Estylos/VFD-MQTT/KICAD_FILES/VFD-MQTT.kicad_sch

## KiCad design KICAD_FILES/VFD-MQTT.kicad_sch (2022-10-23)

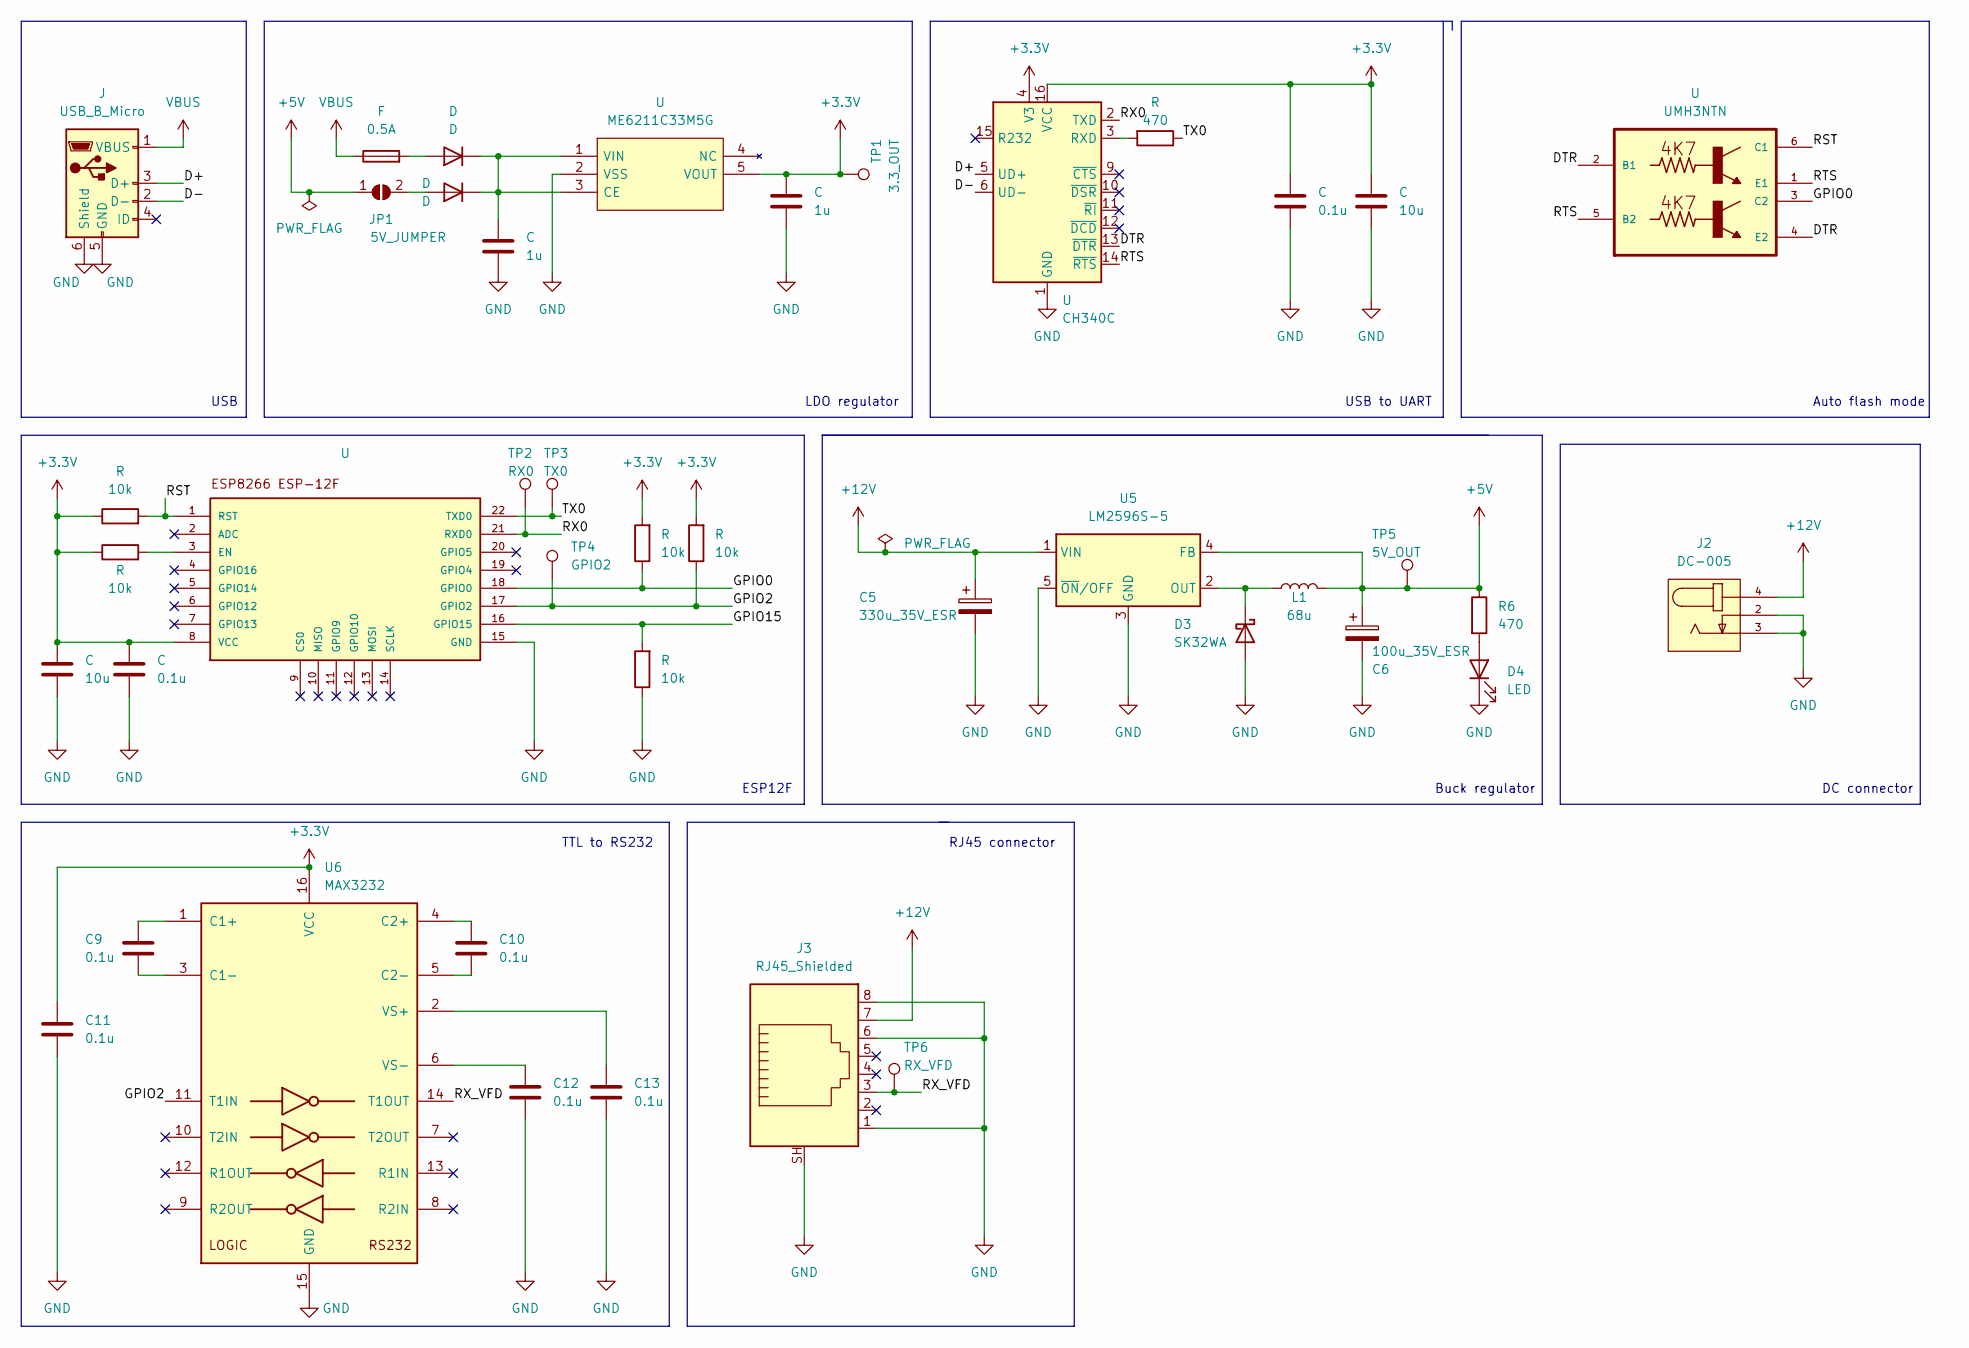
[picture p12: schematic VFD-MQTT.kicad_sch]

Parts:
C: C; C_0805_2012Metric_Pad1.18x1.45mm_HandSolder; LCSC C17024
C5: 330u_35V_ESR; CAP_EEEFP1V331AP_G; LCSC C178582
C6: 100u_35V_ESR; CAP_EEHZK1V101XP_D8; LCSC C454360
C9, C10, C11, C12, C13: 0.1u; C_0805_2012Metric_Pad1.18x1.45mm_HandSolder; LCSC C1711
D: D; SOD-123FL; LCSC C2891324
D3: SK32WA; SOD-123FL; LCSC C183472
D4: LED; LED_0805_2012Metric_Pad1.15x1.40mm_HandSolder; LCSC C434431
F: Fuse; Fuse_0805_2012Metric_Pad1.15x1.40mm_HandSolder; LCSC C2892412
J: USB_B_Micro; USB_Micro-B_Molex-105017-0001; LCSC C136000
J2: DC-005; NINIGI_DC-005; LCSC C16214
J3: RJ45_Shielded; RJ45_Ninigi_GE
JP1: 5V_JUMPER; SolderJumper-2_P1.3mm_Open_Pad1.0x1.5mm
L1: 68u; L_SCDS124T-680M-N; LCSC C329737
R: R; R_0805_2012Metric_Pad1.20x1.40mm_HandSolder; LCSC C2907329
R6: 470; R_0805_2012Metric_Pad1.20x1.40mm_HandSolder; LCSC C2907329
TP1: 3.3_OUT; TestPoint_Pad_D2.0mm
TP2: RX0; TestPoint_Pad_D2.0mm
TP3: TX0; TestPoint_Pad_D2.0mm
TP4: GPIO2; TestPoint_Pad_D2.0mm
TP5: 5V_OUT; TestPoint_Pad_D2.0mm
TP6: RX_VFD; TestPoint_Pad_D2.0mm
U: ME6211C33M5G; SOT95P282X145-5N; Manufacturer_Part_Number ME6211C33M5G; LCSC C82942
U5: LM2596S-5; TO-263-5_TabPin3; LCSC C347421
U6: MAX3232; SOIC-16_3.9x9.9mm_P1.27mm; LCSC C18261

Connections:
+3.3V: C.1, C.2, C11.1, R.1, R.2, TP1.1, U.4 (GPIO16), U.5 (GPIO14), U.8 (VCC), U.16 (GPIO15), U6.16 (VCC)
+5V: C6.1, JP1.1 (A), L1.2, R6.1, TP5.1, U5.4 (FB)
+12V: C5.1, J2.4, J3.7, U5.1 (VIN)
D+: J.3 (D+), U.5 (GPIO14)
D-: J.2 (D-), U.6 (GPIO12)
DTR: U.2 (ADC), U.4 (GPIO16), U.13 (MOSI)
GND: C.1, C.2, C5.2, C6.2, C11.2, C12.2, C13.2, D3.2 (A), D4.1 (K), J.5 (GND), J.6 (Shield), J2.2, J2.3, J3.1, J3.6, J3.8, J3.SH, R.1, U.1 (RST), U.2 (ADC), U.15 (GND), U5.3 (GND), U5.5 (~ON/OFF), U6.15 (GND)
GPIO0: R.1, U.3 (EN), U.18 (GPIO0)
GPIO2: R.1, TP4.1, U.17 (GPIO2), U6.11 (T1IN)
GPIO15: R.2, U.16 (GPIO15)
unnamed: C9.1, U6.1 (C1+)
unnamed: C9.2, U6.3 (C1-)
unnamed: C10.1, U6.5 (C2-)
unnamed: C10.2, U6.4 (C2+)
unnamed: C12.1, U6.6 (VS-)
unnamed: C13.1, U6.2 (VS+)
unnamed: C.1, D.1 (K), U.1 (RST), U.3 (EN)
unnamed: D3.1 (K), L1.1, U5.2 (OUT)
unnamed: D4.2 (A), R6.2
unnamed: D.2 (A), F.2, JP1.2 (B)
unnamed: R.2, U.3 (EN)
RST: R.2, U.1 (RST), U.6 (GPIO12)
RTS: U.1 (RST), U.5 (GPIO14), U.14 (SCLK)
RX0: TP2.1, U.2 (ADC), U.21 (RXD0)
RX_VFD: J3.3, TP6.1, U6.14 (T1OUT)
TX0: R.1, TP3.1, U.22 (TXD0)
VBUS: F.1, J.1 (VBUS)

Notes on the sheet:
USB to UART
Buck regulator
ESP12F
TTL to RS232
LDO regulator
RJ45 connector
DC connector
Auto flash mode
USB
