Estylos/VFD-MQTT/VFD-MQTT-ESP8266/include/credentials.h

// Copyright (c) 2022 Esteban Cadic
// This code is licensed under MIT license (see LICENSE file for details)

#ifndef __CREDENTIALS_H__
#define __CREDENTIALS_H__

#define MQTT_SERVER "IP"
#define MQTT_PORT   1883
#define MQTT_USER   "USER"
#define MQTT_PASS   "PASS"
#define MQTT_CLIENT "vfd-client"
#define MQTT_CHAN   "vfd/message"

#define WIFI_SSID   "SSID"
#define WIFI_PASS   "PASS"

#endif
