Estylos/VFD-MQTT/VFD-MQTT-ESP8266/include/mqtt.h

// Copyright (c) 2022 Esteban Cadic
// This code is licensed under MIT license (see LICENSE file for details)

#ifndef __MQTT_H__
#define __MQTT_H__

// Setup MQTT client
extern void mqttSetup(void);
// MQTT keep alive function
extern void mqttLoop(void);

#endif
